anamitradatta/Integrated-Camera-Trap/Master_Files/test_camera.py

from picamera import PiCamera
from time import sleep
import datetime

camera = PiCamera()
camera.resolution=(3280,2464)
path = '/home/pi/test_photo.jpg'
camera.start_preview()
#sleep(5)
#date = datetime.datetime.now().strftime("%m_%d_%Y_%H_%M_%S_%f")
camera.capture(path)
camera.stop_preview()
